shmoergh/moduleur/modules/02-vco/electronics/ui/schematics/vco-ui.pdf

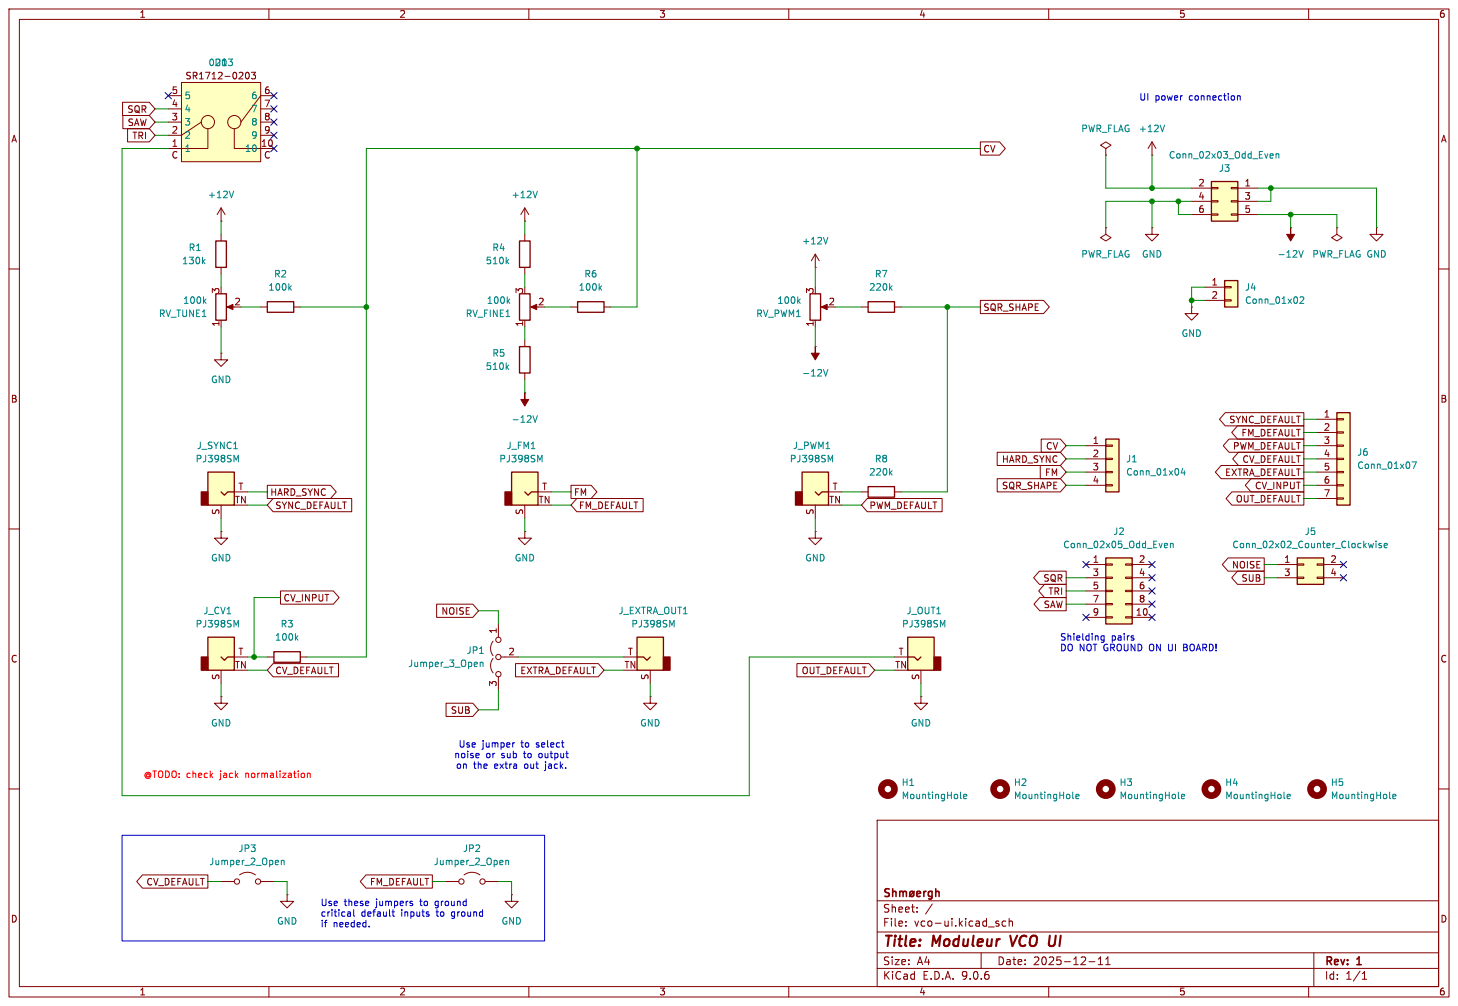
[picture p38: page 1]

Id: 1/1 Title: Moduleur VCO UI File: vco-ui.kicad_sch Sheet: / þÿShmøergh
