shmoergh/moduleur/modules/03-sidechain-mixer/electronics/core/schematics/sidechain-mixer-core.pdf

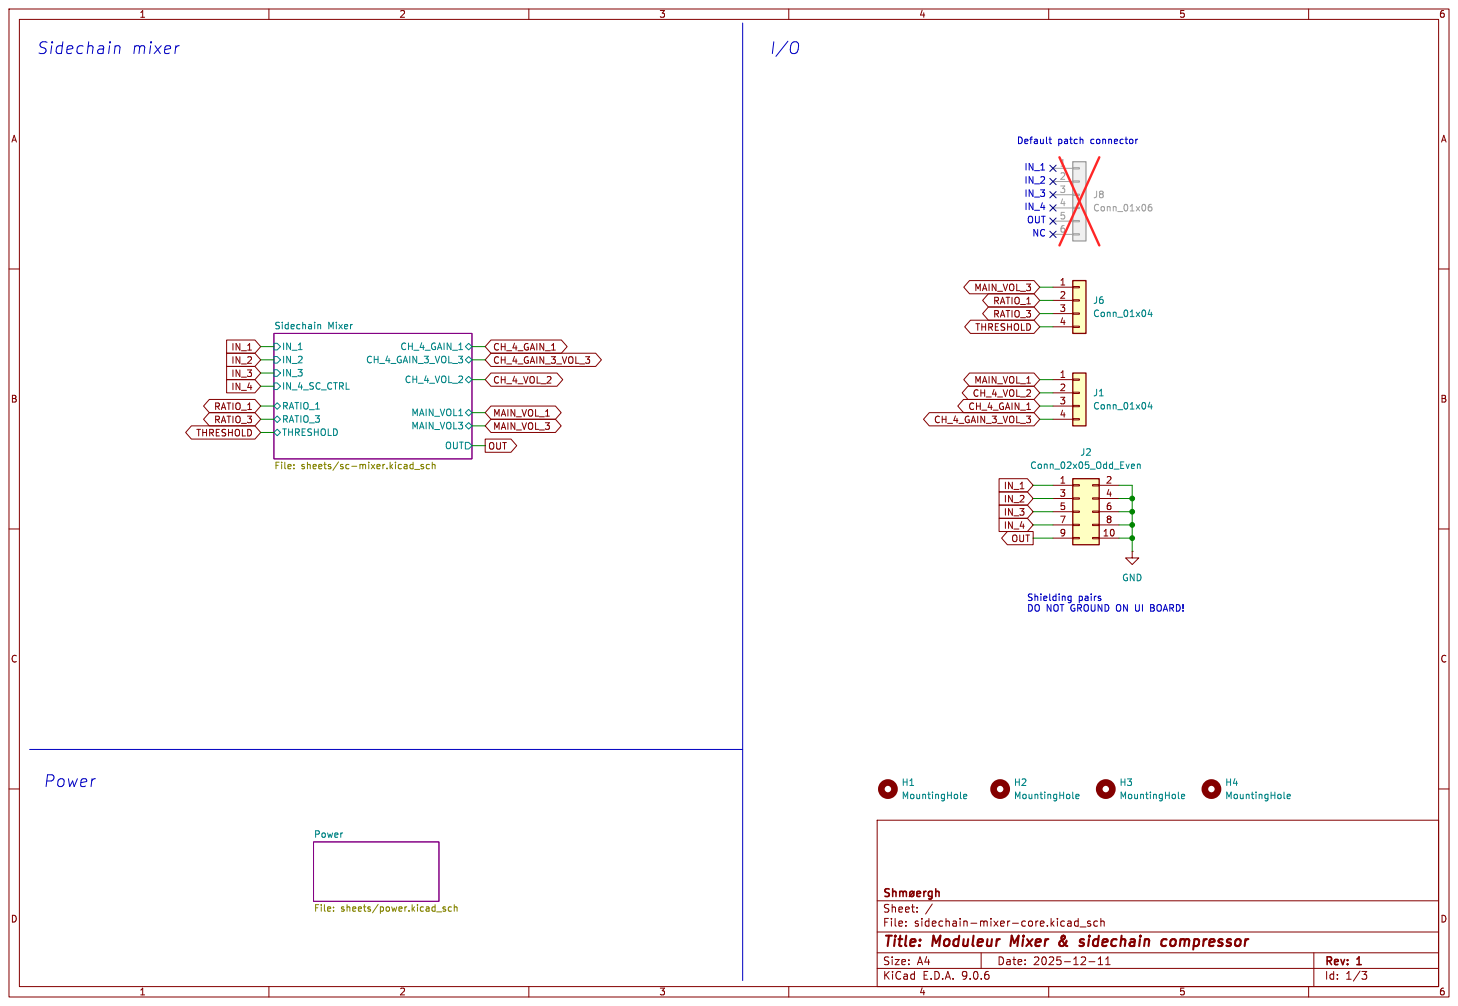
[picture p39: page 1]

Power File: sheets/power.kicad_sch

Id: 1/3 Title: Moduleur Mixer & sidechain compressor File: sidechain-mixer-core.kicad_sch Sheet: / þÿShmøergh

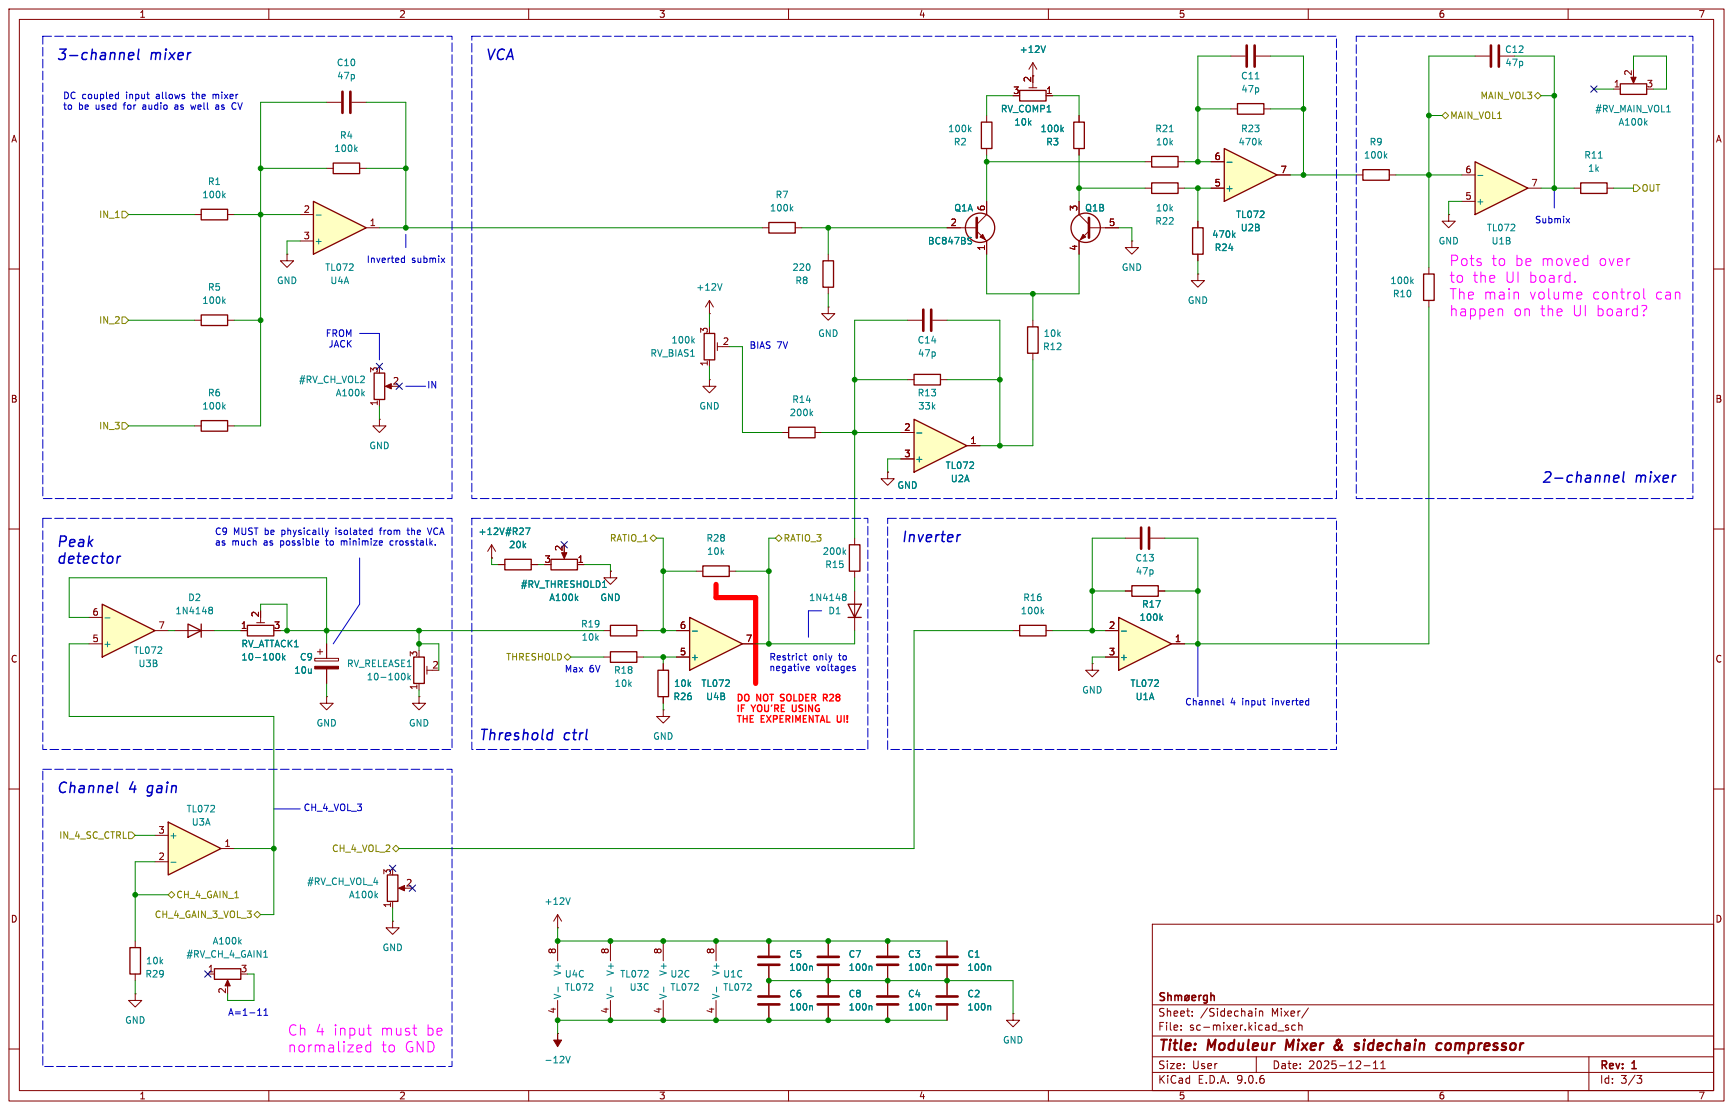
[picture p40: page 2]

DC coupled input allows the mixer

TL072 GND
Pots to be moved over
to the UI board.
The main volume control can
happen on the UI board?

IF YOU'RE USING

Ch 4 input must be

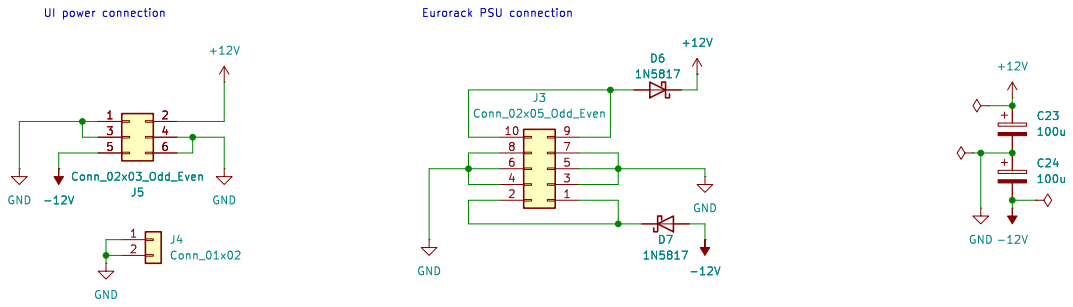
[picture p41: page 3]
