shmoergh/moduleur/modules/03-sidechain-mixer/electronics/ui/schematics/sidechain-mixer-ui.pdf

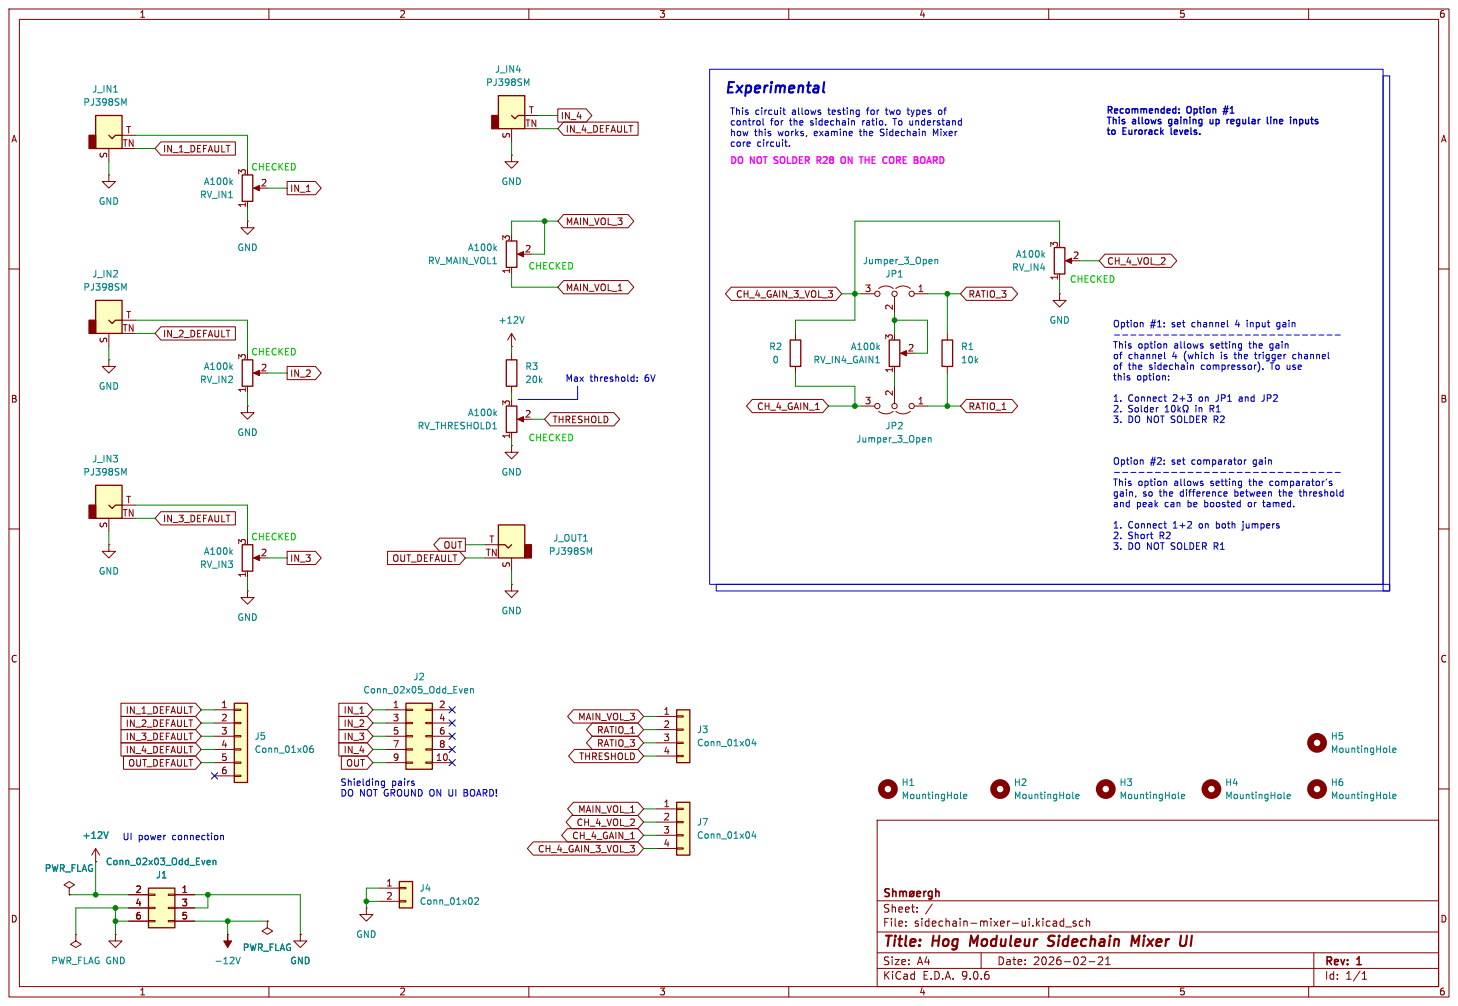
[picture p42: page 1]

3. DO NOT SOLDER R1 Recommended: Option #1 This allows gaining up regular line inputs

3. DO NOT SOLDER R2 CHECKED

---------------------------- This option allows setting the gain

this option: 1. Connect 2+3 on JP1 and JP2

---------------------------- This option allows setting the comparator's

and peak can be boosted or tamed. 1. Connect 1+2 on both jumpers 2. Short R2

Id: 1/1 Title: Hog Moduleur Sidechain Mixer UI File: sidechain-mixer-ui.kicad_sch Sheet: / þÿShmøergh 1
